PeterChu3/Blindr/CAD/TT Motor.SLDPRT

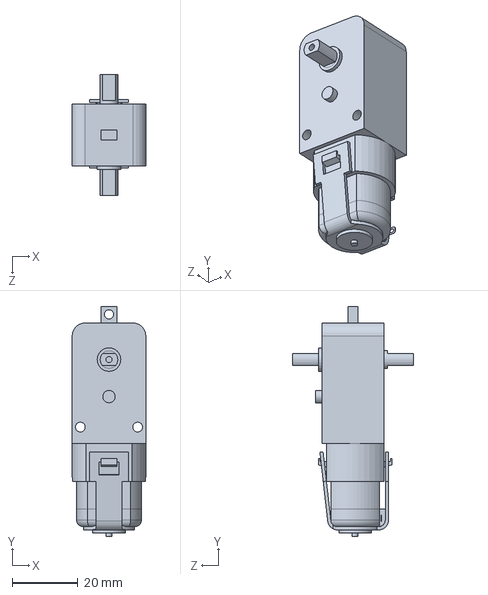
[picture p19: CAD file, 2021-11-10]
CAD/TT Motor.SLDPRT
22.5 x 70.2 x 36.8 mm
