PeterChu3/Blindr/CAD/BlindWand.SLDPRT

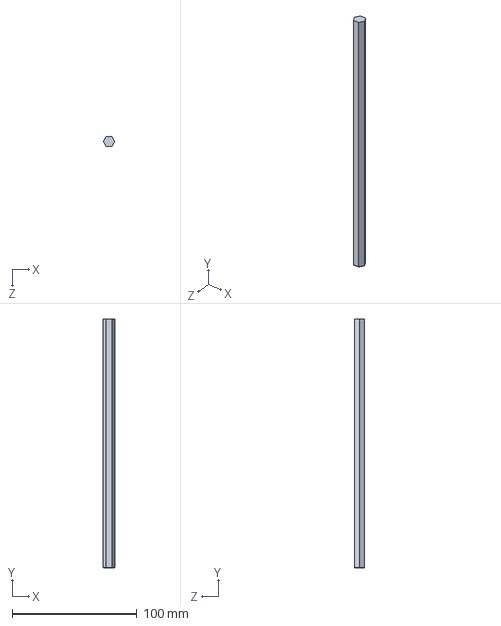
[picture p20: CAD file, 2021-11-10]
CAD/BlindWand.SLDPRT
9.24 x 200.0 x 8.00 mm
